naripok/yawdamper/assets/box.jpeg

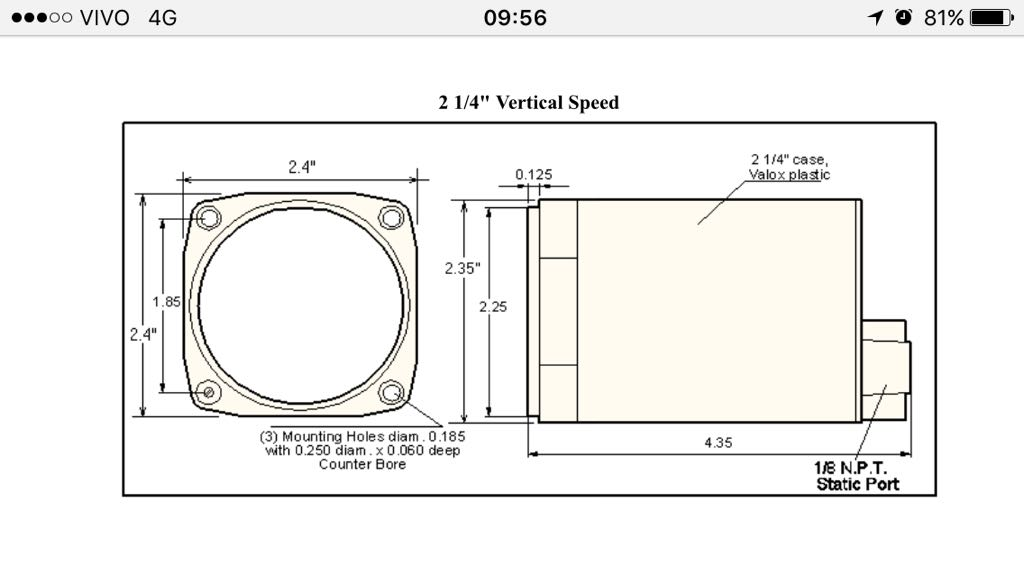
assets/box.jpeg
