naripok/yawdamper/assets/esquema.png

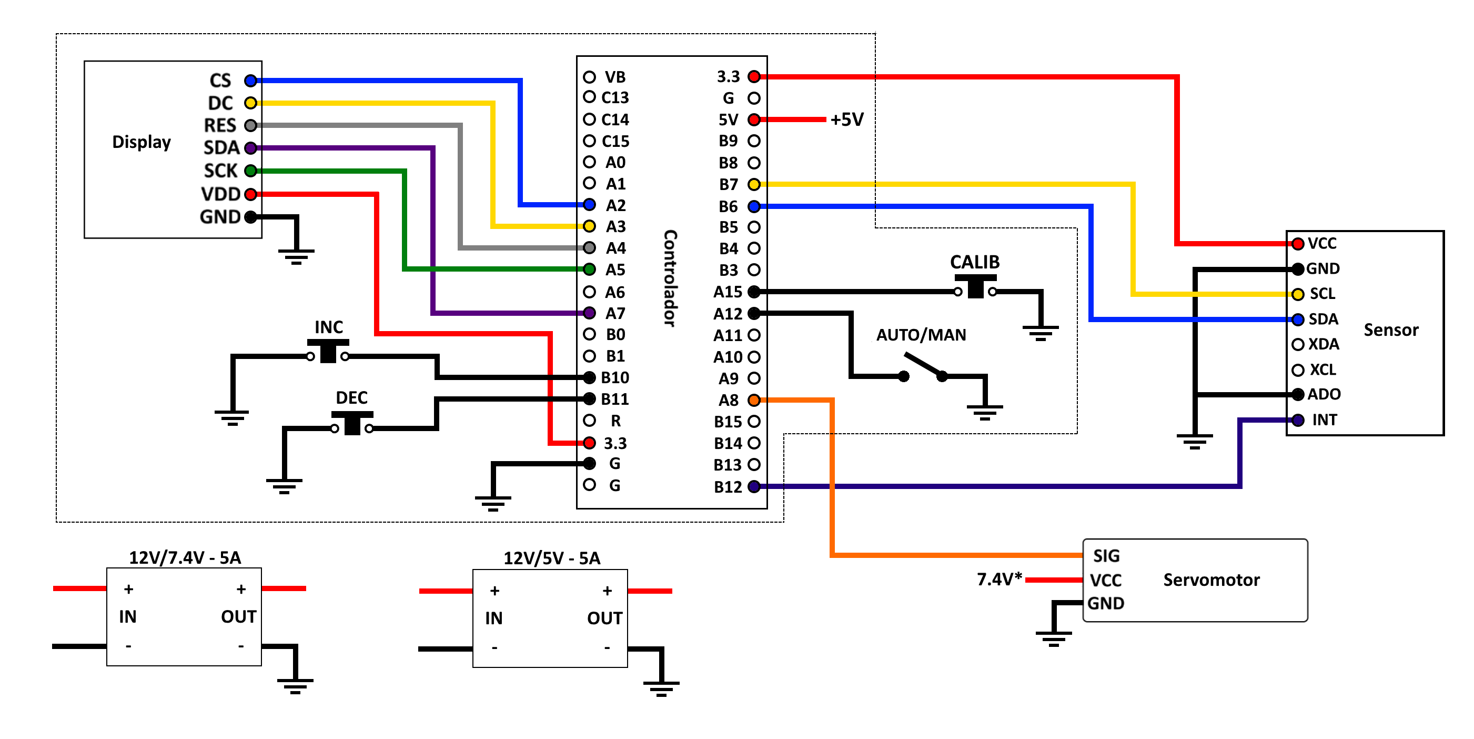
assets/esquema.png
