naripok/yawdamper/Docs/ecra1.png

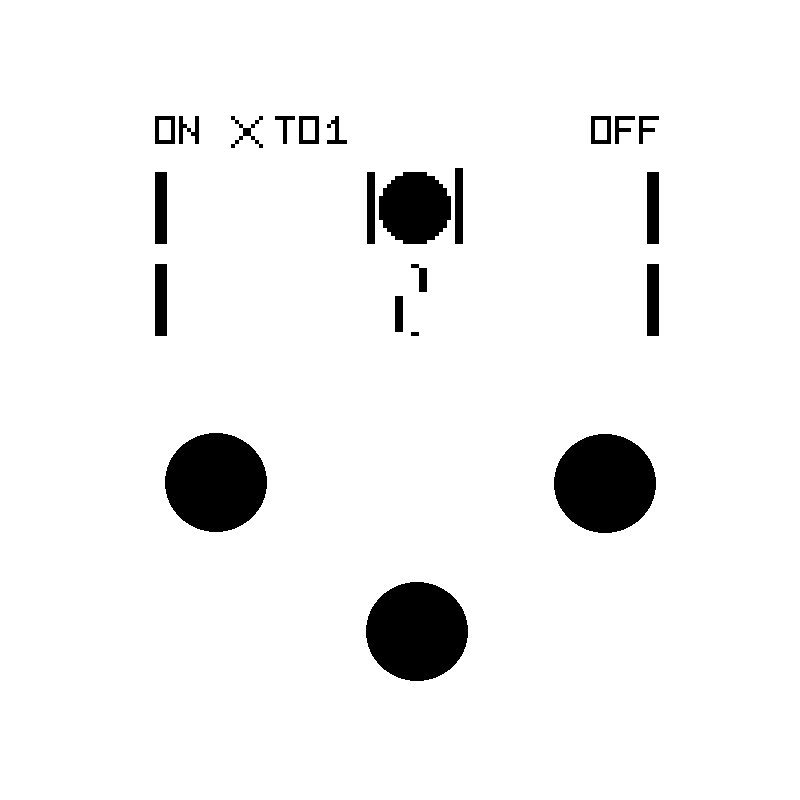
Docs/ecra1.png
